jusdino/lap-keys/firmware/lap_keys/v0.3/v0.3.h

#pragma once

#include "quantum.h"
#include "pointing_device.h"
#include "PMW3360.h"

#define LAYOUT( \
      k00, k01, k02, k03, k04, k05, k06, k07, k08, k09, k010, k011,\
      k10, k11, k12, k13, k14, k15, k16, k17, k18, k19, k110, k111,\
      k20, k21, k22, k23, k24, k25, k26, k27, k28, k29, k210, k211,\
      k30, k31, k32, k33, k34, k35, k36, k37, k38, k39, k310, k311,\
      k40, k41, k42, k43, k44, k45, k46, k47, k48, k49, k410, k411 \
) \
{ \
    { k00, k01, k02, k03, k04, k05, k06, k07, k08, k09, k010, k011 }, \
    { k10, k11, k12, k13, k14, k15, k16, k17, k18, k19, k110, k111 }, \
    { k20, k21, k22, k23, k24, k25, k26, k27, k28, k29, k210, k211 }, \
    { k30, k31, k32, k33, k34, k35, k36, k37, k38, k39, k310, k311 }, \
    { k40, k41, k42, k43, k44, k45, k46, k47, k48, k49, k410, k411 } \
} 
