jusdino/lap-keys/firmware/lap_keys/v0.3/PMW3360.h

/*
  PMW3366.h - Library for interfacing PMW3360 motion sensor module
  Adapted from https://github.com/SunjunKim/PMW3360

  Copyright (c) 2019, Sunjun Kim
  
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
  You should have received a copy of the GNU Lesser General Public
  License along with this library; if not, write to the Free Software
  Foundation, Inc., 51 Franklin St, Fifth Floor, Boston, MA  02110-1301  USA
*/

#pragma once
#include QMK_KEYBOARD_H
#include "spi_master.h"


#define BEGIN_COM spi_start(PMW_SS, false, 3, SPI_DIVISOR); wait_us(1)
#define END_COM   wait_us(1); spi_stop();

#define constrain(amt,low,high) ((amt)<(low)?(low):((amt)>(high)?(high):(amt)))
#define SPI_OPTION (SPI_SPEED_FCPU_DIV_2 | SPI_SCK_LEAD_FALLING | SPI_SAMPLE_TRAILING | SPI_ORDER_MSB_FIRST | SPI_MODE_MASTER)

// Registers
#define REG_Product_ID  0x00
#define REG_Revision_ID 0x01
#define REG_Motion  0x02
#define REG_Delta_X_L 0x03
#define REG_Delta_X_H 0x04
#define REG_Delta_Y_L 0x05
#define REG_Delta_Y_H 0x06
#define REG_SQUAL 0x07
#define REG_Raw_Data_Sum  0x08
#define REG_Maximum_Raw_data  0x09
#define REG_Minimum_Raw_data  0x0A
#define REG_Shutter_Lower 0x0B
#define REG_Shutter_Upper 0x0C
#define REG_Control 0x0D
#define REG_Config1 0x0F
#define REG_Config2 0x10
#define REG_Angle_Tune  0x11
#define REG_Frame_Capture 0x12
#define REG_SROM_Enable 0x13
#define REG_Run_Downshift 0x14
#define REG_Rest1_Rate_Lower  0x15
#define REG_Rest1_Rate_Upper  0x16
#define REG_Rest1_Downshift 0x17
#define REG_Rest2_Rate_Lower  0x18
#define REG_Rest2_Rate_Upper  0x19
#define REG_Rest2_Downshift 0x1A
#define REG_Rest3_Rate_Lower  0x1B
#define REG_Rest3_Rate_Upper  0x1C
#define REG_Observation 0x24
#define REG_Data_Out_Lower  0x25
#define REG_Data_Out_Upper  0x26
#define REG_Raw_Data_Dump 0x29
#define REG_SROM_ID 0x2A
#define REG_Min_SQ_Run  0x2B
#define REG_Raw_Data_Threshold  0x2C
#define REG_Config5 0x2F
#define REG_Power_Up_Reset  0x3A
#define REG_Shutdown  0x3B
#define REG_Inverse_Product_ID  0x3F
#define REG_LiftCutoff_Tune3  0x41
#define REG_Angle_Snap  0x42
#define REG_LiftCutoff_Tune1  0x4A
#define REG_Motion_Burst  0x50
#define REG_LiftCutoff_Tune_Timeout 0x58
#define REG_LiftCutoff_Tune_Min_Length  0x5A
#define REG_SROM_Load_Burst 0x62
#define REG_Lift_Config 0x63
#define REG_Raw_Data_Burst  0x64
#define REG_LiftCutoff_Tune2  0x65

/*
Raw burst data structure: 
  BYTE[00] = Motion    = if the 7th bit is 1, a motion is detected.
         ==> 7 bit: MOT (1 when motion is detected)
         ==> 3 bit: 0 when chip is on surface / 1 when off surface
  BYTE[01] = Observation  
  BYTE[02] = Delta_X_L = dx (LSB)
  BYTE[03] = Delta_X_H = dx (MSB) 
  BYTE[04] = Delta_Y_L = dy (LSB)
  BYTE[05] = Delta_Y_H = dy (MSB)
  BYTE[06] = SQUAL     = Surface Quality register, max 0x80
                       - Number of features on the surface = SQUAL * 8
  BYTE[07] = Raw_Data_Sum   = It reports the upper byte of an 18‐bit counter which sums all 1296 raw data in the current frame;
                             * Avg value = Raw_Data_Sum * 1024 / 1296
  BYTE[08] = Maximum_Raw_Data  = Max raw data value in current frame, max=127
  BYTE[09] = Minimum_Raw_Data  = Min raw data value in current frame, max=127
  BYTE[10] = Shutter_Upper     = Shutter LSB
  BYTE[11] = Shutter_Lower     = Shutter MSB, Shutter = shutter is adjusted to keep the average raw data values within normal operating ranges

Struct description
- PMW3360_DATA.isMotion      : bool, True if a motion is detected. 
- PMW3360_DATA.isOnSurface   : bool, True when a chip is on a surface 
- PMW3360_DATA.dx, data.dy   : integer, displacement on x/y directions.
- PMW3360_DATA.SQUAL         : byte, Surface Quality register, max 0x80
                       * Number of features on the surface = SQUAL * 8
- PMW3360_DATA.rawDataSum    : byte, It reports the upper byte of an 18‐bit counter 
                       which sums all 1296 raw data in the current frame;
                       * Avg value = Raw_Data_Sum * 1024 / 1296
- PMW3360_DATA.maxRawData    : byte, Max/Min raw data value in current frame, max=127
  PMW3360_DATA.minRawData
- PMW3360_DATA.shutter       : unsigned int, shutter is adjusted to keep the average
                       raw data values within normal operating ranges.
*/
struct PMW3360_DATA
{
 int8_t motion;
 bool isMotion;        // True if a motion is detected. 
 bool isOnSurface;     // True when a chip is on a surface 
 int16_t dx;               // displacement on x directions. Unit: Count. (CPI * Count = Inch value)
 int8_t mdx;
 int16_t dy;               // displacement on y directions.
 int8_t mdy;
 // uint8_t SQUAL;           // Surface Quality register, max 0x80. Number of features on the surface = SQUAL * 8
 // uint8_t rawDataSum;      // It reports the upper byte of an 18‐bit counter which sums all 1296 raw data in the current frame; * Avg value = Raw_Data_Sum * 1024 / 1296
 // uint8_t maxRawData;      // Max raw data value in current frame, max=127
 // uint8_t minRawData;      // Min raw data value in current frame, max=127
 // int16_t shutter; // unit: clock cycles of the internal oscillator. shutter is adjusted to keep the average raw data values within normal operating ranges.
}; 
#ifdef SPI_DEBUG
void print_byte(uint8_t byte);
#endif
bool pmw_begin(void);
void set_cpi(uint32_t cpi);
struct PMW3360_DATA read_burst(void);
uint8_t adns_read_reg(uint8_t reg_addr);
void adns_write_reg(uint8_t reg_addr, uint8_t data);
void adns_upload_firmware(void);
bool check_signature(void);
